Martchus/AudioBoard/src Matrixprojekt/MusikDing/animation.cpp

/*
Grundsystem, umrechnung FFT-Daten, kalibrierung
*/

#include <avr/io.h>
#include <avr/pgmspace.h>
#include <string.h>
#include <avr/eeprom.h>
#include <stdlib.h>

#include "animation.h"
#include "CFFT.h"
#include "ffft.h"
#include "CLED.h"
#include "CSSD1306.h"
#include "CInput.h"
#include "animations.h"
#include "global.h"

extern CLED led;
extern CSSD1306 lcd;
extern CInput input;

// nutzdaten
uint16_t bands_l[ANIM_BAND_NUM], bands_r[ANIM_BAND_NUM];
uint16_t amplitude_l, amplitude_r;
uint8_t beats, bpm_h, bpm_m, bpm_l, bpm_all;
uint8_t fft_bucket_h_l, fft_bucket_h_r, fft_bucket_l_l, fft_bucket_l_r;

// arbeitsdaten
#define SPECTRUM_MA_NUM			16			// berechnung MA übers spektrum
uint16_t ma_spectrum_low[SPECTRUM_MA_NUM], ma_spectrum_mid[SPECTRUM_MA_NUM], ma_spectrum_high[SPECTRUM_MA_NUM];
uint8_t ma_spectrum_wpos, ma_spectrum_rpos;
#define BPM_WMA_NUM				4			// berechnung WMA der bpm

#define ANIM_INPUT_PER_SECOND	20		// anzahl aufrufe anim_input pro sekunde

uint8_t anim_buffer[ANIM_BUFFER_SIZE];
void (*anim_frame_func)(void);

bands_calibration_t b_calib;
bands_calibration_t EEMEM b_calib_eeprom;

// flags für system
uint8_t anim_flags, anim_cur = 0;
uint32_t anim_next_tick = 0, anim_change_delay = 60000;

anim_list_t anim_list[ANIM_LIST_NUM] = {
					{"Spektrum Mono", anim_monospektrum_init, anim_monospektrum_step},
					{"Spektrum Stereo", anim_stereospektrum_init, anim_stereospektrum_step},
					{"Partikel 1", anim_partikel1_init, anim_partikel1_step},
					{"Kreisding", anim_kreisding_init, anim_kreisding_step},
					{"Punkte", anim_punkte_init, anim_punkte_step},
					{"Tropfen", anim_tropfen_init, anim_tropfen_step},
					{"Amplitude 1", anim_amplitude1_init, anim_amplitude1_step}
									};

void anim_init()
{	
	memset(bands_l, 0, sizeof(uint16_t) * ANIM_BAND_NUM);
	memset(bands_r, 0, sizeof(uint16_t) * ANIM_BAND_NUM);

	memset(ma_spectrum_low, 0, sizeof(uint16_t) * SPECTRUM_MA_NUM);
	memset(ma_spectrum_mid, 0, sizeof(uint16_t) * SPECTRUM_MA_NUM);
	memset(ma_spectrum_high, 0, sizeof(uint16_t) * SPECTRUM_MA_NUM);
	ma_spectrum_rpos = 0;
	ma_spectrum_wpos = 0;
		
	eeprom_read_block((void*)&b_calib, (void*)&b_calib_eeprom, sizeof(bands_calibration_t));
	
	if(b_calib.ident != ANIM_CALIB_IDENT)
	{
		memset(&b_calib, 0, sizeof(bands_calibration_t));
		b_calib.bands_calib_l[0] = 6209;
		b_calib.bands_calib_l[1] = 3991;
		b_calib.bands_calib_l[2] = 37;
		b_calib.bands_calib_l[3] = 34;
		b_calib.bands_calib_l[4] = 56;
		b_calib.bands_calib_l[5] = 100;
		b_calib.bands_calib_l[6] = 146;
		
		b_calib.bands_calib_r[0] = 6099;
		b_calib.bands_calib_r[1] = 3886;
		b_calib.bands_calib_r[2] = 116;
		b_calib.bands_calib_r[3] = 141;
		b_calib.bands_calib_r[4] = 213;
		b_calib.bands_calib_r[5] = 424;
		b_calib.bands_calib_r[6] = 649;
		
		b_calib.amplitude_l = 46;
		b_calib.amplitude_r = 165;
	}
	
	beats = 0;
	bpm_h = 0;
	bpm_m = 0;
	bpm_l = 0;
	
	anim_frame_func = NULL;
	
	anim_flags = 0;
}

void anim_frame()
{
	if(anim_flags & ANIM_FLAG_CHANGE)
	{
		if(systick >= anim_next_tick)
		{
			anim_next_tick = systick + anim_change_delay;
			
			if(anim_flags & ANIM_FLAG_RANDOM)
			{
				if(anim_flags & ANIM_FLAG_NOREPEAT)
				{
					uint8_t temp;
					
					do {
						temp = rand() % ANIM_LIST_NUM;
					} while(temp == anim_cur);
					
					anim_cur = temp;
				}
				else
				{
					anim_cur = rand() % ANIM_LIST_NUM;
				}
			}
			else
			{
				anim_cur = (anim_cur + 1) % ANIM_LIST_NUM;
			}
			
			if(anim_list[anim_cur].init)
			{
				anim_list[anim_cur].init();
			}
	
			anim_frame_func = anim_list[anim_cur].step;			
		}
	}
	
	if(anim_frame_func)
	{
		anim_frame_func();
	}
}

/*
64 buckets, 250Hz/bucket -> 7 Bänder
0	0		250		0
1	250		500		1
2	500		1000	2 ... 3
3	1000	2000	4 ... 7
4	2000	4000	8 ... 15
5	4000	8000	16 ... 31
6	8000	ende	32 ... 63
*/
void anim_inputData(fft_result_t *left, fft_result_t *right)
{
	uint32_t temp_r, temp_l, temp_h, temp_m;
	uint8_t i;
	static uint8_t cnt = 0, h_cnt = 0, m_cnt = 0, l_cnt = 0, all_cnt = 0;
	
	// bänder zusammenfassen
	bands_l[0] = left->spectrum[0];
	bands_r[0] = right->spectrum[0];
	
	bands_l[1] = left->spectrum[1];
	bands_r[1] = right->spectrum[1];
	
	temp_l = 0;
	temp_r = 0;
	for(i = 2; i <= 3; i++)
	{
		temp_l += left->spectrum[i];
		temp_r += right->spectrum[i];
	}
	bands_l[2] = temp_l / 2;
	bands_r[2] = temp_r / 2;
	
	temp_l = 0;
	temp_r = 0;
	for(i = 4; i <= 7; i++)
	{
		temp_l += left->spectrum[i];
		temp_r += right->spectrum[i];
	}
	bands_l[3] = temp_l / 4;
	bands_r[3] = temp_r / 4;
	
	temp_l = 0;
	temp_r = 0;
	for(i = 8; i <= 15; i++)
	{
		temp_l += left->spectrum[i];
		temp_r += right->spectrum[i];
	}
	bands_l[4] = temp_l / 8;
	bands_r[4] = temp_r / 8;
	
	temp_l = 0;
	temp_r = 0;
	for(i = 16; i <= 31; i++)
	{
		temp_l += left->spectrum[i];
		temp_r += right->spectrum[i];
	}
	bands_l[5] = temp_l / 16;
	bands_r[5] = temp_r / 16;
	
	temp_l = 0;
	temp_r = 0;
	for(i = 32; i <= 63; i++)
	{
		temp_l += left->spectrum[i];
		temp_r += right->spectrum[i];
	}
	bands_l[6] = temp_l / 28;
	bands_r[6] = temp_r / 28;
	
	// höchste/tiefste buckets suchen
	fft_bucket_h_l = 0;
	fft_bucket_h_r = 0;
	fft_bucket_l_r = 255;
	fft_bucket_l_l = 255;
	
	temp_h = left->spectrum[0];
	temp_l = right->spectrum[0];
	temp_m = 0xFFFFFFFF;
	temp_r = 0xFFFFFFFF;
	for(i = 0; i < (FFT_N / 2); i++)
	{
		if(left->spectrum[i] > temp_h)
		{
			temp_h = left->spectrum[i];
			fft_bucket_h_l = i;
		}
		if(right->spectrum[i] > temp_l)
		{
			temp_l = right->spectrum[i];
			fft_bucket_h_r = i;
		}
		
		if(left->spectrum[i] < temp_m)
		{
			temp_m = left->spectrum[i];
			fft_bucket_l_l = i;
		}
		if(right->spectrum[i] < temp_r)
		{
			temp_r = left->spectrum[i];
			fft_bucket_l_r = i;
		}
	}
	
	// amplitude merken
	amplitude_l = left->adc_max - left->adc_min;
	amplitude_r = right->adc_max - right->adc_min;
	
	// moving mean übers spectrum
	temp_l = 0;
	for(i = 0; i < 3; i++)
	{
		temp_l += (left->spectrum[i] + right->spectrum[i]) / 2;
	}
	ma_spectrum_low[ma_spectrum_wpos] = temp_l / 3;
	
	temp_l = 0;
	for(i = 3; i < 20; i++)
	{
		temp_l += (left->spectrum[i] + right->spectrum[i]) / 2;
	}
	ma_spectrum_mid[ma_spectrum_wpos] = temp_l / 17;

	temp_l = 0;
	for(i = 20; i < 63; i++)
	{
		temp_l += (left->spectrum[i] + right->spectrum[i]) / 2;
	}
	ma_spectrum_high[ma_spectrum_wpos] = temp_l / 43;
	
	ma_spectrum_rpos = ma_spectrum_wpos;
	ma_spectrum_wpos = (ma_spectrum_wpos + 1) % SPECTRUM_MA_NUM;
	
	// abgleich/kalibrierung
	for(i = 0; i < ANIM_BAND_NUM; i++)
	{
		if(bands_l[i] > b_calib.bands_calib_l[i])
		{
			bands_l[i] -= b_calib.bands_calib_l[i];
		}
		else
		{
			bands_l[i] = 0;
		}
		
		if(bands_r[i] > b_calib.bands_calib_r[i])
		{
			bands_r[i] -= b_calib.bands_calib_r[i];
		}
		else
		{
			bands_r[i] = 0;
		}
	}
	
	if(amplitude_l > b_calib.amplitude_l)
	{
		amplitude_l -= b_calib.amplitude_l;
	}
	else
	{
		amplitude_l = 0;
	}
	
	if(amplitude_r > b_calib.amplitude_r)
	{
		amplitude_r -= b_calib.amplitude_r;
	}
	else
	{
		amplitude_r = 0;
	}
	
	// primitive beat erkennung
	temp_h = 0;
	temp_l = 0;
	temp_m = 0;
	
	for(i = 0; i < SPECTRUM_MA_NUM; i++)
	{
		temp_h += ma_spectrum_high[i];
		temp_m += ma_spectrum_mid[i];
		temp_l += ma_spectrum_low[i];
	}
	
	temp_h /= SPECTRUM_MA_NUM;
	temp_m /= SPECTRUM_MA_NUM;
	temp_l /= SPECTRUM_MA_NUM;
	
	
	beats = 0;
	if(ma_spectrum_high[ma_spectrum_rpos] > (uint16_t)((float)temp_h * 2.0f))
	{
		beats |= BEAT_HIGH;
		h_cnt++;
	}
	
	if(ma_spectrum_mid[ma_spectrum_rpos] > (uint16_t)((float)temp_m * 1.8f))
	{
		beats |= BEAT_MID;
		m_cnt++;
	}
	
	if(ma_spectrum_low[ma_spectrum_rpos] > (uint16_t)((float)temp_l * 1.5f))
	{
		beats |= BEAT_LOW;
		l_cnt++;
	}
	
	if(beats)
	{
		all_cnt++;
	}
	
	cnt++;
	if(cnt >= (ANIM_INPUT_PER_SECOND * 2))
	{
		bpm_l = ((bpm_l * (BPM_WMA_NUM - 1)) + (l_cnt * 30)) / BPM_WMA_NUM;
		l_cnt = 0;
		
		bpm_m = ((bpm_m * (BPM_WMA_NUM - 1)) + (m_cnt * 30)) / BPM_WMA_NUM;
		m_cnt = 0;
		
		bpm_h = ((bpm_h * (BPM_WMA_NUM - 1)) + (h_cnt * 30)) / BPM_WMA_NUM;
		h_cnt = 0;
		
		bpm_all = ((bpm_all * (BPM_WMA_NUM - 1)) + (all_cnt * 30)) / BPM_WMA_NUM;
		all_cnt = 0;
		
		cnt = 0;
	}
	
#ifdef __INPUT_DEBUG__
	// !!! debug
	{
		char str[4];
		static uint16_t zoom = 20000;
			
		zoom += input.getEnc() * 1000;
		
		memset(str, 0, 4);
		if(beats & BEAT_HIGH)
		{
			str[0] = 'H';
		}
		if(beats & BEAT_MID)
		{
			str[1] = 'M';
		}
		if(beats & BEAT_LOW)
		{
			str[2] = 'L';
		}
		
		lcd.graph2(bands_l, bands_r, 7, zoom, 5);
		lcd.print(0, 0, "%s", anim_list[anim_cur].name);
#ifdef	__APS_DEBUG__
		lcd.print(1, LCD_STYLE_NOCLEAR, "FPS:%02d  SPS:%02d   BPM", __fps, __sps);
#else
		lcd.print(1, LCD_STYLE_NOCLEAR, "                 BPM", __fps, __sps);
#endif
		lcd.print(2, LCD_STYLE_NOCLEAR | LCD_STYLE_RIGHT, "H:%03d", bpm_h);
		lcd.print(3, LCD_STYLE_NOCLEAR | LCD_STYLE_RIGHT, "M:%03d", bpm_m);
		lcd.print(4, LCD_STYLE_NOCLEAR | LCD_STYLE_RIGHT, "T:%03d", bpm_l);
		lcd.print(5, LCD_STYLE_NOCLEAR | LCD_STYLE_RIGHT, "A:%03d", bpm_all);
		lcd.print(7, LCD_STYLE_NOCLEAR | LCD_STYLE_RIGHT, "%u", zoom);
	}
#endif
}

//
// "animation" für kalibration
//

#define ANIM_CALIB_CNT		32
#define ANIM_CALIB_ROUND	5

typedef struct
{
	uint8_t cnt, round;
	uint32_t s_left[ANIM_CALIB_ROUND][ANIM_BAND_NUM], s_right[ANIM_CALIB_ROUND][ANIM_BAND_NUM];
	uint32_t a_left[ANIM_CALIB_ROUND], a_right[ANIM_CALIB_ROUND];
	uint16_t max_a_left, max_a_right, max_s_left[ANIM_BAND_NUM], max_s_right[ANIM_BAND_NUM];
} calib_anim_t;

void anim_frameCalibration()
{
	calib_anim_t *d = (calib_anim_t*)anim_buffer;
	uint8_t i;
	
	for(i = 0; i < ANIM_BAND_NUM; i++)
	{
		d->s_left[d->round][i] += bands_l[i];
		if(bands_l[i] > d->max_s_left[i])
		{
			d->max_s_left[i] = bands_l[i];
		}
		
		d->s_right[d->round][i] += bands_r[i];
		if(bands_r[i] > d->max_s_right[i])
		{
			d->max_s_right[i] = bands_r[i];
		}
	}
	
	d->a_left[d->round] += amplitude_l;
	if(amplitude_l > d->max_a_left)
	{
		d->max_a_left = amplitude_l;
	}
	
	d->a_right[d->round] += amplitude_r;
	if(amplitude_r > d->max_a_right)
	{
		d->max_a_right = amplitude_r;
	}
	
	d->cnt++;
	
	if(d->cnt >= ANIM_CALIB_CNT)
	{
		// runde beendet
		d->cnt = 0;
		
		d->a_left[d->round] /= ANIM_CALIB_CNT;
		d->a_right[d->round] /= ANIM_CALIB_CNT;
		
		for(i = 0; i < ANIM_BAND_NUM; i++)
		{
			d->s_left[d->round][i] /= ANIM_CALIB_CNT;
			d->s_right[d->round][i] /= ANIM_CALIB_CNT;
		}
				
		d->round++;
		if(d->round >= ANIM_CALIB_ROUND)
		{
			// fertig, auswerten
			uint32_t s_temp_l[ANIM_BAND_NUM], s_temp_r[ANIM_BAND_NUM], a_temp_l, a_temp_r;
			uint8_t j;
			
			memset(s_temp_l, 0, sizeof(uint32_t) * ANIM_BAND_NUM);
			memset(s_temp_r, 0, sizeof(uint32_t) * ANIM_BAND_NUM);
			a_temp_l = 0;
			a_temp_r = 0;
			
			for(i = 0; i < ANIM_CALIB_ROUND; i++)
			{
				a_temp_l += d->a_left[i];
				a_temp_r += d->a_right[i];
				
				for(j = 0; j < ANIM_BAND_NUM; j++)
				{
					s_temp_l[j] += d->s_left[i][j];
					s_temp_r[j] += d->s_right[i][j];
				}
			}
			
			a_temp_l /= ANIM_CALIB_ROUND;
			a_temp_r /= ANIM_CALIB_ROUND;
			for(i = 0; i < ANIM_BAND_NUM; i++)
			{
				s_temp_l[i] /= ANIM_CALIB_ROUND;
				s_temp_r[i] /= ANIM_CALIB_ROUND;
			}
			
			b_calib.ident = ANIM_CALIB_IDENT;
			b_calib.amplitude_l = (7 * d->max_a_left + a_temp_l) / 8;
			b_calib.amplitude_r = (7 * d->max_a_right + a_temp_r) / 8;
			for(i = 0; i < ANIM_BAND_NUM; i++)
			{
				b_calib.bands_calib_l[i] = (7 * d->max_s_left[i] + s_temp_l[i]) / 8;
				b_calib.bands_calib_r[i] = (7 * d->max_s_right[i] + s_temp_r[i]) / 8;
			}
			
			
			// !!!
//			eeprom_write_block((void*)&b_calib, (void*)&b_calib_eeprom, sizeof(bands_calibration_t));
			
			anim_frame_func = NULL;
		}
	}
}

void anim_startCalibration()
{
	calib_anim_t *d = (calib_anim_t*)anim_buffer;
	
	memset(&b_calib, 0, sizeof(bands_calibration_t));
	memset(d, 0, sizeof(calib_anim_t));
	led.clear();
	led.update();
	
	anim_frame_func = anim_frameCalibration;
}

void anim_start(uint16_t num)
{
	if(num >= ANIM_LIST_NUM)
	{
		return;
	}
	
	if(anim_list[num].init)
	{
		anim_list[num].init();
	}
	
	anim_cur = num;
	anim_frame_func = anim_list[num].step;
}

void anim_setFlags(uint8_t f)
{
	anim_flags = f;
}

void anim_setDelay(uint32_t d)
{
	anim_change_delay = d;
}
