Martchus/AudioBoard/src Matrixprojekt/MusikDing/animations.h

#ifndef ANIMATIONS_H_
#define ANIMATIONS_H_

void anim_monospektrum_init();
void anim_monospektrum_step();

void anim_stereospektrum_init();
void anim_stereospektrum_step();

void anim_partikel1_init();
void anim_partikel1_step();

void anim_kreisding_init();
void anim_kreisding_step();

void anim_punkte_init();
void anim_punkte_step();

void anim_tropfen_init();
void anim_tropfen_step();

void anim_amplitude1_init();
void anim_amplitude1_step();

#endif /* ANIMATIONS_H_ */
